m351351/Velocity-Based-Training/VBT_Turtinen_tervonen/src/Motion.h

#ifndef MOTION_H
#define MOTION_H

#include <Arduino.h>
#include "Arduino_BMI270_BMM150.h"
#include "Exercise.h"

// Julkiset funktiot
void setupMotion();
void handleMotion();
void calibrateMotion();

extern float velocity; // Julkinen muuttuja, jotta BLEHandler tai main voi lukea nopeuden
extern ExerciseType currentExercise;
extern bool inRep;
#endif
