m351351/Velocity-Based-Training/VBT_Turtinen_tervonen/src/Battery.h

#ifndef BATTERY_H
#define BATTERY_H

#include <Arduino.h>

uint8_t readBatteryPercent(float* outVoltage = nullptr, int* outRaw = nullptr);
void updateBattery(bool doNotify);
void handleBattery();

#endif
